cajunpanda/gameboy-hifi-audio/hardware/agb/agb-hifi-audio-fpc/agb-hifi-audio-fpc.kicad_sch

## KiCad design hardware/agb/agb-hifi-audio-fpc/agb-hifi-audio-fpc.kicad_sch (2026-06-22)

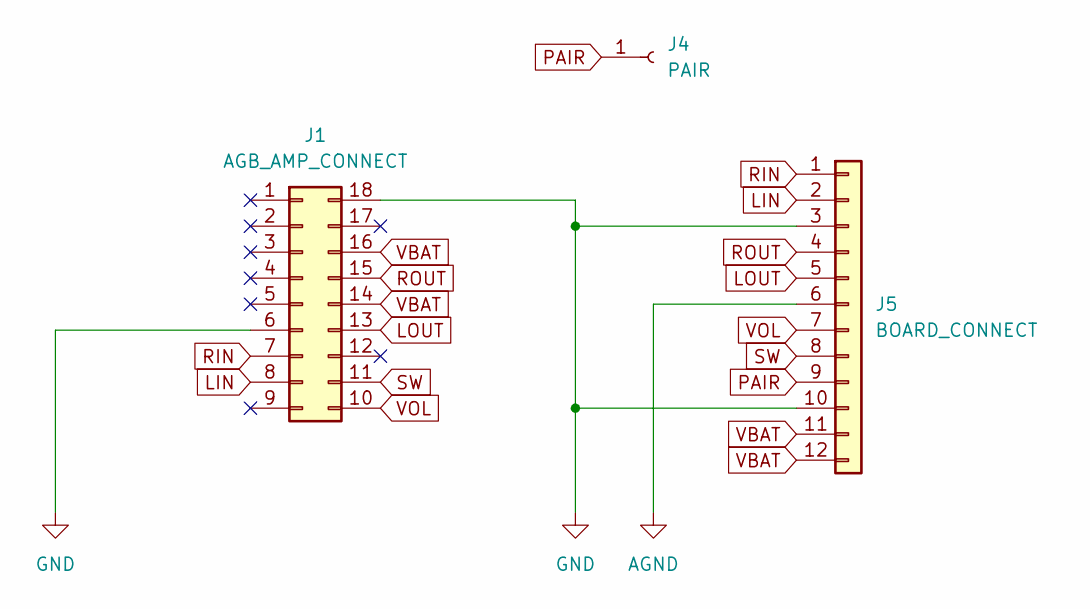
[picture p13: schematic agb-hifi-audio-fpc.kicad_sch]

Parts:
J1: AGB_AMP_CONNECT; AGB AMP CONNECT
J4: PAIR; SolderWirePad_1x01_SMD_1x2mm
J5: BOARD_CONNECT; FPC-Tail-12pos-0.5mm-FH12A

Connections:
AGND: J5.6
GND: J1.6, J1.18, J5.3, J5.10
LIN: J1.8, J5.2
LOUT: J1.13, J5.5
PAIR: J4.1, J5.9
RIN: J1.7, J5.1
ROUT: J1.15, J5.4
SW: J1.11, J5.8
VBAT: J1.14, J1.16, J5.11, J5.12
VOL: J1.10, J5.7
