cajunpanda/gameboy-hifi-audio/hardware/agb/agb-hifi-audio-pcb/agb-hifi-audio-pcb.kicad_sch

## KiCad design hardware/agb/agb-hifi-audio-pcb/agb-hifi-audio-pcb.kicad_sch (2026-07-22)

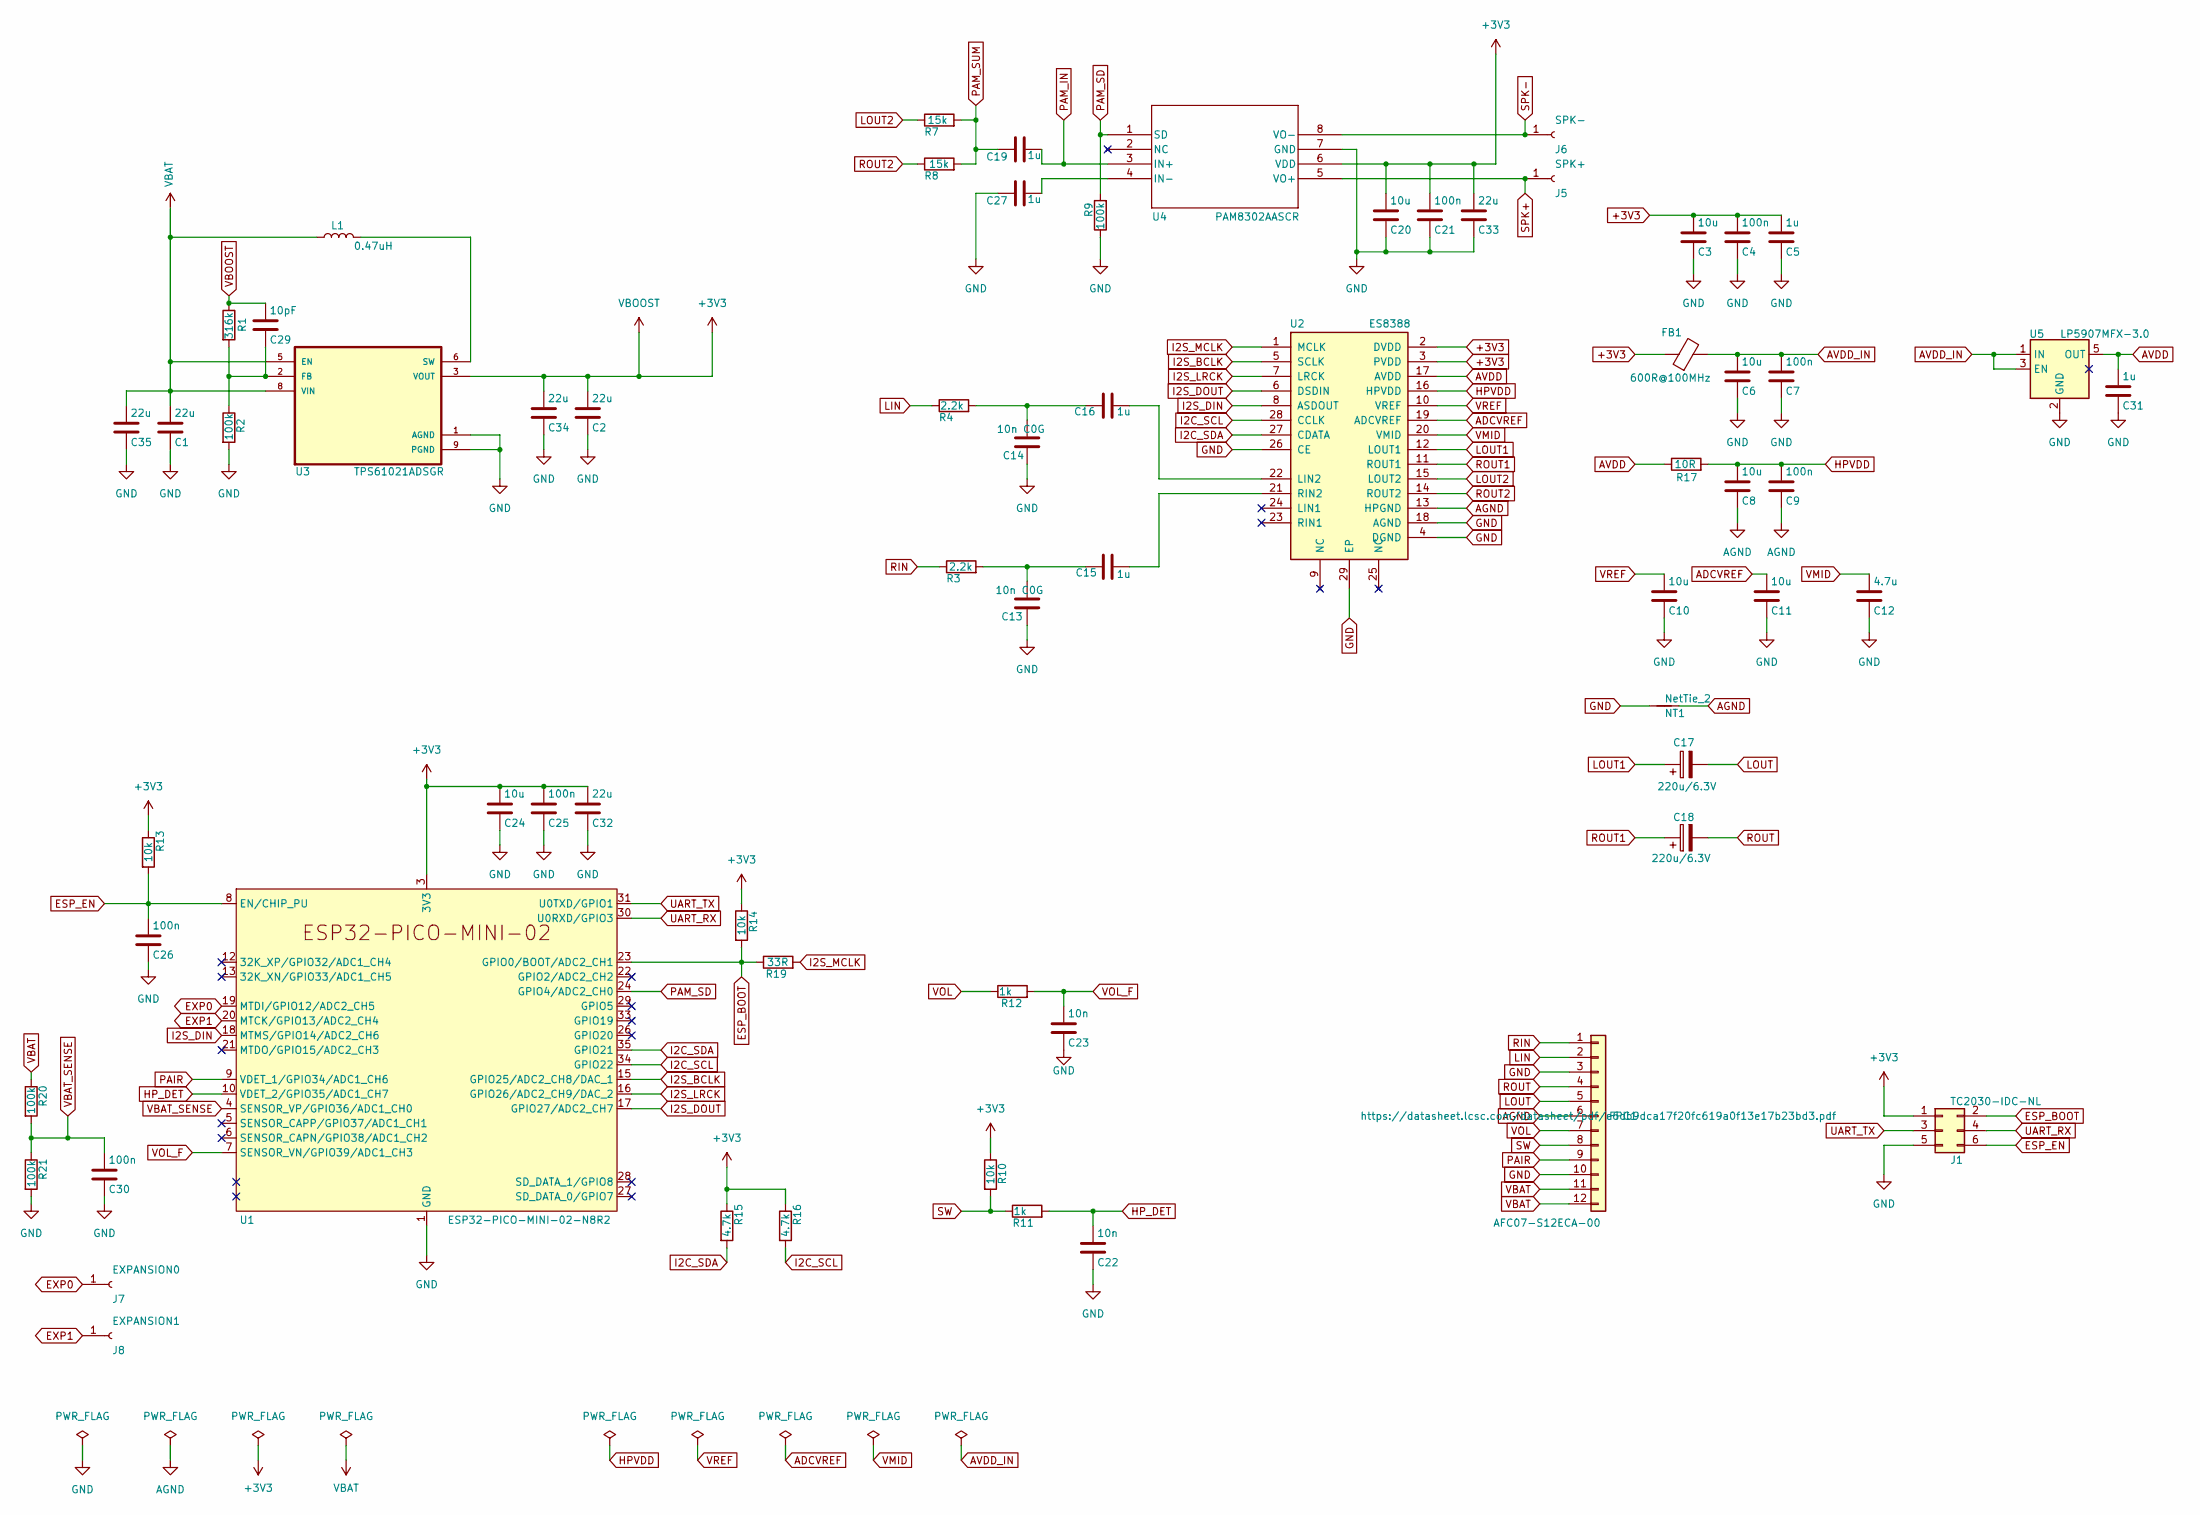
[picture p14: schematic agb-hifi-audio-pcb.kicad_sch]

Parts:
C1, C2, C32, C33, C34, C35: 22u; C_0805_2012Metric_Pad1.18x1.45mm_HandSolder; MPN CL21A226MAQNNNE; LCSC C45783
C3, C6, C8, C10, C11, C20, C24: 10u; C_0402_1005Metric_Pad0.74x0.62mm_HandSolder; MPN CL05A106MQ5NUNC; LCSC C15525
C4, C7, C9, C21, C25, C26, C30: 100n; C_0402_1005Metric_Pad0.74x0.62mm_HandSolder; MPN CL05B104KO5NNNC; LCSC C1525
C5, C15, C16, C19, C27, C31: 1u; C_0402_1005Metric_Pad0.74x0.62mm_HandSolder; MPN CL05A105KA5NQNC; LCSC C52923
C12: 4.7u; C_0402_1005Metric_Pad0.74x0.62mm_HandSolder; MPN CL05A475MP5NRNC; LCSC C23733
C13, C14: 10n C0G; C_0402_1005Metric_Pad0.74x0.62mm_HandSolder; MPN GRM1555C1E103JE01D; LCSC C3855387
C17, C18: 220u/6.3V; CP_EIA-3528-21_Kemet-B_HandSolder; MPN T520B227M006ATE045; LCSC C254404
C22, C23: 10n; C_0402_1005Metric_Pad0.74x0.62mm_HandSolder; MPN CL05B103KB5NNNC; LCSC C15195
C29: 10pF; C_0402_1005Metric_Pad0.74x0.62mm_HandSolder; MPN CL05C100JB5NNNC; LCSC C32949
FB1: 600R@100MHz; L_0402_1005Metric_Pad0.77x0.64mm_HandSolder; MPN BLM15AG601SN1D; LCSC C76884
FPC1: AFC07-S12ECA-00; FPC-SMD_12P-P0.50_AFC07-S12ECA-00; MPN AFC07-S12ECA-00; LCSC C262585
J1: TC2030-IDC-NL; Tag-Connect_TC2030-IDC-NL_2x03_P1.27mm_Vertical
J5: SPK+; SolderWirePad_1x01_SMD_1x2mm
J6: SPK-; SolderWirePad_1x01_SMD_1x2mm
J7: EXPANSION0; SolderWirePad_1x01_SMD_1x2mm
J8: EXPANSION1; SolderWirePad_1x01_SMD_1x2mm
L1: 0.47uH; L_Sunlord_SWPA252012S; MPN WIP252012P-R47ML; LCSC C964119
NT1: NetTie_2; NetTie-2_SMD_Pad0.2mm
R1: 316k; R_0402_1005Metric_Pad0.72x0.64mm_HandSolder; MPN 0402WGF3163TCE; LCSC C25777
R2, R9, R20, R21: 100k; R_0402_1005Metric_Pad0.72x0.64mm_HandSolder; MPN 0402WGF1003TCE; LCSC C25741
R3, R4: 2.2k; R_0402_1005Metric_Pad0.72x0.64mm_HandSolder; MPN 0402WGF2201TCE; LCSC C25879
R7, R8: 15k; R_0402_1005Metric_Pad0.72x0.64mm_HandSolder; MPN 0402WGF1502TCE; LCSC C25756
R10, R13, R14: 10k; R_0402_1005Metric_Pad0.72x0.64mm_HandSolder; MPN 0402WGF1002TCE; LCSC C25744
R11, R12: 1k; R_0402_1005Metric_Pad0.72x0.64mm_HandSolder; MPN 0402WGF1001TCE; LCSC C11702
R15, R16: 4.7k; R_0402_1005Metric_Pad0.72x0.64mm_HandSolder; MPN 0402WGF4701TCE; LCSC C25900
R17: 10R; R_0402_1005Metric_Pad0.72x0.64mm_HandSolder; MPN 0402WGF100JTCE; LCSC C25077
R19: 33R; R_0402_1005Metric_Pad0.72x0.64mm_HandSolder; MPN 0402WGF330JTCE; LCSC C25105
U1: ESP32-PICO-MINI-02-N8R2; MODULE_ESP32-PICO-MINI-02; MPN ESP32-PICO-MINI-02-N8R2; LCSC C2980306
U2: ES8388; QFN-28-1EP_4x4mm_P0.45mm_EP2.4x2.4mm_ThermalVias; MPN ES8388; LCSC C365736
U3: TPS61021ADSGR; DSG0008A_TEX; MPN TPS61021ADSGR; LCSC C193037
U4: PAM8302AASCR; MSOP-8_3x3mm_P0.65mm; MPN PAM8302AASCR; LCSC C113367
U5: LP5907MFX-3.0; SOT-23-5_HandSoldering; MPN LP5907MFX-3.0/NOPB; LCSC C475492

Connections:
+3V3: C1.1, C1.2, C2.1, C2.2, C3.1, C3.2, C4.1, C4.2, C5.1, C5.2, C6.1, C6.2, C7.1, C7.2, C8.1, C8.2, C9.1, C9.2, C10.1, C10.2, C11.1, C11.2, C12.1, C12.2, C13.2, C14.2, C20.1, C20.2, C21.1, C21.2, C22.2, C23.2, C24.1, C24.2, C25.1, C25.2, C26.2, C27.1, C30.2, C31.2, C32.1, C32.2, C33.1, C33.2, C34.1, C34.2, C35.1, C35.2, FB1.1, FB1.2, J1.1, J1.5, L1.1, R2.2, R9.1, R10.1, R13.1, R14.1, R15.1, R16.1, R17.2, R21.2, U1.1 (GND), U1.2 (GND), U1.3 (3V3), U1.11 (GND), U1.14 (GND), U1.36 (GND), U1.37 (GND), U1.38 (GND), U1.39 (GND), U1.40 (GND), U1.41 (GND), U1.42 (GND), U1.43 (GND), U1.44 (GND), U1.45 (GND), U1.46 (GND), U1.47 (GND), U1.48 (GND), U1.49 (GND), U1.50 (GND), U1.51 (GND), U1.52 (GND), U1.53 (GND), U1.54 (GND), U1.55 (GND), U1.56 (GND), U1.57 (GND), U1.58 (GND), U1.59 (GND), U1.60 (GND), U1.61 (GND), U2.2 (DVDD), U2.3 (PVDD), U2.10 (VREF), U2.16 (HPVDD), U2.19 (ADCVREF), U2.20 (VMID), U3.1 (AGND), U3.3 (VOUT), U3.4 (VOUT), U3.5 (EN), U3.8 (VIN), U3.9 (PGND), U4.6 (VDD), U4.7 (GND), U5.1 (IN), U5.2 (GND), U5.3 (EN)
AGND: FPC1.6, NT1.2, U2.13 (HPGND)
AVDD: C31.1, R17.1, U2.17 (AVDD), U5.5 (OUT)
ESP_BOOT: J1.2, R14.2, R19.1, U1.23 (GPIO0/BOOT/ADC2_CH1)
ESP_EN: C26.1, J1.6, R13.2, U1.8 (EN/CHIP_PU)
EXP0: J7.1, U1.19 (MTDI/GPIO12/ADC2_CH5)
EXP1: J8.1, U1.20 (MTCK/GPIO13/ADC2_CH4)
GND: FPC1.3, FPC1.10, NT1.1, U2.4 (DGND), U2.18 (AGND), U2.26 (CE), U2.29 (EP)
HP_DET: C22.1, R11.2, U1.10 (VDET_2/GPIO35/ADC1_CH7)
I2C_SCL: R16.2, U1.34 (GPIO22), U2.28 (CCLK)
I2C_SDA: R15.2, U1.35 (GPIO21), U2.27 (CDATA)
I2S_BCLK: U1.15 (GPIO25/ADC2_CH8/DAC_1), U2.5 (SCLK)
I2S_DIN: U1.18 (MTMS/GPIO14/ADC2_CH6), U2.8 (ASDOUT)
I2S_DOUT: U1.17 (GPIO27/ADC2_CH7), U2.6 (DSDIN)
I2S_LRCK: U1.16 (GPIO26/ADC2_CH9/DAC_2), U2.7 (LRCK)
I2S_MCLK: R19.2, U2.1 (MCLK)
LIN: FPC1.2, R4.1
LOUT: C17.2, FPC1.5
LOUT1: C17.1, U2.12 (LOUT1)
LOUT2: R7.1, U2.15 (LOUT2)
unnamed: C13.1, C15.1, R3.2
unnamed: C14.1, C16.1, R4.2
unnamed: C15.2, U2.21 (RIN2)
unnamed: C16.2, U2.22 (LIN2)
unnamed: C27.2, U4.4 (IN-)
unnamed: C29.2, R1.2, R2.1, U3.2 (FB)
unnamed: L1.2, U3.6 (SW), U3.7 (SW)
PAIR: FPC1.9, U1.9 (VDET_1/GPIO34/ADC1_CH6)
PAM_IN: C19.2, U4.3 (IN+)
PAM_SD: R9.2, U1.24 (GPIO4/ADC2_CH0), U4.1 (SD)
PAM_SUM: C19.1, R7.2, R8.2
RIN: FPC1.1, R3.1
ROUT: C18.2, FPC1.4
ROUT1: C18.1, U2.11 (ROUT1)
ROUT2: R8.1, U2.14 (ROUT2)
SPK+: J5.1, U4.5 (VO+)
SPK-: J6.1, U4.8 (VO-)
SW: FPC1.8, R10.2, R11.1
UART_RX: J1.4, U1.30 (U0RXD/GPIO3)
UART_TX: J1.3, U1.31 (U0TXD/GPIO1)
VBAT: FPC1.11, FPC1.12, R20.1
VBAT_SENSE: C30.1, R20.2, R21.1, U1.4 (SENSOR_VP/GPIO36/ADC1_CH0)
VBOOST: C29.1, R1.1
VOL: FPC1.7, R12.1
VOL_F: C23.1, R12.2, U1.7 (SENSOR_VN/GPIO39/ADC1_CH3)
