cajunpanda/gameboy-hifi-audio/firmware/src/dsp.c

#include "dsp.h"

#include <math.h>
#include <string.h>

#include "esp_log.h"
#include "dsps_biquad.h"
#include "dsps_biquad_gen.h"

#include "settings.h"
#include "sfx.h"

static const char *TAG = "dsp";

#define PIPE_RATE   44100.0f
#define MAX_BLOCK   256             // == audio_pipeline READ_FRAMES

// Speaker EQ band centre frequencies, voiced for the small GBA driver: a low
// shelf to tame bass the driver can't reproduce, a presence peak for clarity,
// and a high shelf for air. Band gains come from settings (dB).
#define F_BASS      (150.0f  / PIPE_RATE)
#define F_MID       (2500.0f / PIPE_RATE)
#define F_TREBLE    (5000.0f / PIPE_RATE)
#define Q_SHELF     0.707f
#define Q_PEAK      1.0f

// Per-sample one-pole smoothing for the volume gain gives click-free steps
// (~5 ms time constant at 44.1 kHz).
#define VOL_SMOOTH  0.005f

// Speaker EQ (stereo): coefficients {b0,b1,b2,a1,a2} plus a separate delay line
// {w0,w1} per channel ([0]=L, [1]=R). The local DAC path is stereo (HP), so each
// channel's biquads keep their own state.
static float s_coef_bass[5], s_coef_mid[5], s_coef_treble[5];
static float s_w_bass[2][2], s_w_mid[2][2], s_w_treble[2][2];

// Bluetooth EQ (stereo): same band coefficients, independent gains, and a
// separate delay line per channel ([0]=L, [1]=R). Each biquad instance keeps its
// own state.
static float s_bt_coef_bass[5], s_bt_coef_mid[5], s_bt_coef_treble[5];
static float s_btw_bass[2][2], s_btw_mid[2][2], s_btw_treble[2][2];

// Noise-reduction filters on the local capture path (per-channel biquad state,
// [0]=L [1]=R). Each is bypassed when its corner/center is 0 Hz; the notch is a
// fixed deep null with tunable center + Q. Tuned per GBA via the `nr` command.
static float s_nr_hpf[5], s_nr_lpf[5], s_nr_notch[5];
static float s_nr_w_hpf[2][2], s_nr_w_lpf[2][2], s_nr_w_notch[2][2];
static bool  s_nr_hpf_on, s_nr_lpf_on, s_nr_notch_on;

// Downward expander / noise gate on the local path. Envelope from each block's
// post-EQ RMS -- not peak: BLE TX bursts couple sub-ms clicks into the ADC that
// peak up to ~-37 dBFS (above any usable threshold) but carry almost no block
// energy (RMS <= -45 dBFS), while real program holds RMS near its peak (square
// waves have ~no crest factor). RMS keying gates the clicks and lets the amp
// mute engage; peak keying let every click punch through and reset the mute
// hold. Applied gain ramps per sample with a fast attack, slow release so the
// floor fades out in quiet passages without chattering. Off when threshold 0.
#define GATE_ATTACK   0.02f       // ~1 ms to open
#define GATE_RELEASE  0.0004f     // ~55 ms to close
#define GATE_MUTE_HOLD 24         // ~140 ms of sustained silence before amp mute
static bool  s_gate_on;
static float s_gate_thresh_db, s_gate_range_db;
static float s_gate_target = 1.0f;   // per-block target gain (linear)
static float s_gate_gain   = 1.0f;   // smoothed applied gain
static int   s_gate_silence = 0;     // consecutive silent blocks (amp-mute hold)
static bool  s_gate_muting = false;  // speaker-amp mute state (sustained silence)
static void (*s_gate_mute_cb)(bool) = NULL;  // notified on mute-state change

// Bluetooth-path noise reduction. The A2DP stream needs the same capture cleanup
// the local path gets: without it the raw GBA floor (hum + hiss) was fed straight
// into the SBC encoder, whose low-level rendering was audible as a distinct
// digital hash on the sink. Reuses the shared s_nr_* coefficients and gate
// thresholds (same tuning, same per-GBA `nr` settings) but keeps its own
// per-channel delay lines and its own smoothed expander gain, so the BT stream
// filters/gates independently of the local speaker path. No amp-mute here: the
// sink has its own amp, so gating the signal to silence is enough.
static float s_bt_nr_w_hpf[2][2], s_bt_nr_w_lpf[2][2], s_bt_nr_w_notch[2][2];
static float s_bt_gate_target = 1.0f;   // per-block target gain (linear)
static float s_bt_gate_gain   = 1.0f;   // smoothed applied gain

// The BT stream hard-mutes on its own threshold, more aggressive than the local
// path's expander/amp-mute, for two reasons: (1) the SBC encoder renders even a
// few-dB residual floor as audible digital hash, so BT must reach true digital
// silence where the local analog path tolerates a low floor; (2) during A2DP
// streaming the radio's conducted TX transients lift the captured floor toward
// the local gate threshold (they no longer defeat the detector outright now
// that it keys on RMS, but the margin is thin) -- this threshold sits clear of
// the floor + those transients. Below it for GATE_MUTE_HOLD blocks, the BT
// program is driven to digital zero. Runtime-tunable per GBA (settings
// nr_bt_mute_db / `nr btmute`): set it too high and quiet program (e.g. engine
// hum) gets swallowed on BT while playing fine locally; too low and the floor
// hash returns. 0 dBFS disables the hard mute (the expander still runs).
static int   s_bt_gate_silence = 0;   // consecutive below-threshold blocks (BT mute hold)
static bool  s_bt_mute_on   = true;   // BT hard mute enabled (nr_bt_mute_db < 0)
static float s_bt_mute_db   = -40.0f; // BT hard-mute threshold, dBFS

static uint32_t s_last_gen = 0xffffffffu;
// Which local-path EQ profile is live: false = Speaker EQ (HP unplugged),
// true = Headphone EQ (HP plugged). Set by dsp_set_hp_plugged(); s_hp_dirty
// forces a coeff recompute + delay-line reset on the next block even though the
// settings generation didn't change.
static volatile bool s_hp_plugged = false;
static volatile bool s_hp_dirty   = false;
static bool     s_eq_on;                 // active local EQ enabled (speaker or HP)
static bool     s_bt_eq_on;              // bluetooth EQ enabled
static float    s_vol_target = 0.0f;     // speaker volume gain target
static float    s_cur_gain = 0.0f;       // smoothed speaker volume (starts muted)
static float    s_bt_vol_target = 1.0f;  // bluetooth volume gain target
static float    s_bt_cur_gain = 1.0f;    // smoothed bluetooth volume
static float    s_sfx_gain = 0.0f;       // linear cue-mix gain (0 = sfx disabled)

// Boot startup-chime intro. While the startup clip plays, the live GBA passthrough
// (program) is muted so the clean full chime plays alone -- no doubling with the
// truncated live chime the codec picks up once the amp comes on -- and the chime
// tracks the volume wheel instead of sitting at the fixed cue level. s_intro_prog
// runs 0 (program muted, chime at wheel volume) during the intro and ramps to 1
// (program live, cues at the fixed feedback level) when the clip ends. Default 1.0
// means "no intro": normal operation is byte-for-byte unchanged. The latch is
// armed by dsp_begin_intro() before the audio task starts, then advanced only by
// the audio task in dsp_process_local(), so no locking is needed.
#define INTRO_RELEASE   0.0006f   // ~38 ms per-sample ramp back to passthrough at chime end
#define INTRO_END_GAP   12        // cue-inactive blocks (~70 ms) that mark the clip done (tolerates FIFO underruns)
#define INTRO_START_MAX 260       // ~1.5 s: if the clip never starts (missing file), give up and unmute
static bool  s_intro_active   = false;   // arming latch (clip in progress)
static bool  s_intro_cue_seen = false;   // the clip actually started
static int   s_intro_gap      = 0;       // consecutive cue-inactive blocks since start
static int   s_intro_blocks   = 0;       // blocks since arming (start-timeout)
static float s_intro_prog     = 1.0f;    // smoothed program/chime-mode gain (1 = normal)

static inline int16_t sat16(float x)
{
    if (x > 32767.0f)  x = 32767.0f;
    if (x < -32768.0f) x = -32768.0f;
    return (int16_t)lrintf(x);
}

static float db_to_lin(float db) { return powf(10.0f, db / 20.0f); }

// esp-dsp's dsps_biquad_gen_peakingEQ_f32 takes no gain argument, so the
// RBJ-cookbook peaking coefficients for the mid band are computed by hand
// (esp-dsp still runs the filter via dsps_biquad_f32). f is normalized (Fc/Fs);
// output coeffs = {b0,b1,b2,a1,a2} normalized so a0 = 1.
static void gen_peaking(float *c, float f, float gain_db, float q)
{
    float A     = powf(10.0f, gain_db / 40.0f);
    float w0    = 2.0f * (float)M_PI * f;
    float cw    = cosf(w0);
    float alpha = sinf(w0) / (2.0f * q);
    float a0    = 1.0f + alpha / A;
    c[0] = (1.0f + alpha * A) / a0;   // b0
    c[1] = (-2.0f * cw)       / a0;   // b1
    c[2] = (1.0f - alpha * A) / a0;   // b2
    c[3] = (-2.0f * cw)       / a0;   // a1
    c[4] = (1.0f - alpha / A) / a0;   // a2
}

// Recompute everything that depends on settings, only when the generation
// counter changes (coefficient generation is the expensive part). Both process
// functions call this at the top of a block; the first one does the work, the
// second sees an unchanged generation and skips. Keeps a single consistent
// snapshot per block across the speaker and BT paths.
static void maybe_recompute(void)
{
    uint32_t gen = settings_generation();
    bool hp_switch = s_hp_dirty;
    if (gen == s_last_gen && !hp_switch) return;
    s_hp_dirty = false;

    gbhifi_settings_t s;
    settings_get(&s);

    // Local-path EQ: pick the profile by which output is live (the DAC drives
    // only one; the speaker amp is muted when HP is plugged), then build the band
    // coefficients from that profile's gains. Speaker EQ voices the small GBA
    // driver; Headphone EQ is independent (flat by default).
    bool   l_on     = s_hp_plugged ? s.eq_hp_enabled   : s.eq_enabled;
    int8_t l_bass   = s_hp_plugged ? s.eq_hp_bass_db   : s.eq_bass_db;
    int8_t l_mid    = s_hp_plugged ? s.eq_hp_mid_db    : s.eq_mid_db;
    int8_t l_treble = s_hp_plugged ? s.eq_hp_treble_db : s.eq_treble_db;
    dsps_biquad_gen_lowShelf_f32 (s_coef_bass,   F_BASS,   (float)l_bass,   Q_SHELF);
    gen_peaking                  (s_coef_mid,    F_MID,    (float)l_mid,    Q_PEAK);
    dsps_biquad_gen_highShelf_f32(s_coef_treble, F_TREBLE, (float)l_treble, Q_SHELF);
    s_eq_on = l_on;

    // On a profile swap (HP plug/unplug) the delay lines hold the old filter's
    // state; flush them so the new curve doesn't ring. A settings-only change
    // (volume/EQ tweak) leaves them alone to avoid a click on every edit.
    if (hp_switch) {
        memset(s_w_bass,   0, sizeof(s_w_bass));
        memset(s_w_mid,    0, sizeof(s_w_mid));
        memset(s_w_treble, 0, sizeof(s_w_treble));
    }

    // Bluetooth EQ coefficients (same bands, independent gains).
    dsps_biquad_gen_lowShelf_f32 (s_bt_coef_bass,   F_BASS,   (float)s.eq_bt_bass_db,   Q_SHELF);
    gen_peaking                  (s_bt_coef_mid,    F_MID,    (float)s.eq_bt_mid_db,    Q_PEAK);
    dsps_biquad_gen_highShelf_f32(s_bt_coef_treble, F_TREBLE, (float)s.eq_bt_treble_db, Q_SHELF);
    s_bt_eq_on = s.eq_bt_enabled;

    // Noise-reduction filters (local path). Normalized freq = Hz / PIPE_RATE;
    // Butterworth HPF/LPF (Q=0.707), and a deep (-40 dB) notch at the tunable
    // center + Q. Zero a filter's delay line while it is off so toggling it on
    // later starts from a clean state instead of ringing on stale samples.
    s_nr_hpf_on   = s.nr_hpf_hz   > 0 && s.nr_hpf_hz   < PIPE_RATE / 2;
    s_nr_lpf_on   = s.nr_lpf_hz   > 0 && s.nr_lpf_hz   < PIPE_RATE / 2;
    s_nr_notch_on = s.nr_notch_hz > 0 && s.nr_notch_hz < PIPE_RATE / 2;
    // Zero both the local and BT delay lines when a filter is off so toggling it
    // on later starts clean on each path.
    if (s_nr_hpf_on)
        dsps_biquad_gen_hpf_f32(s_nr_hpf, (float)s.nr_hpf_hz / PIPE_RATE, Q_SHELF);
    else { memset(s_nr_w_hpf, 0, sizeof(s_nr_w_hpf));
           memset(s_bt_nr_w_hpf, 0, sizeof(s_bt_nr_w_hpf)); }
    if (s_nr_lpf_on)
        dsps_biquad_gen_lpf_f32(s_nr_lpf, (float)s.nr_lpf_hz / PIPE_RATE, Q_SHELF);
    else { memset(s_nr_w_lpf, 0, sizeof(s_nr_w_lpf));
           memset(s_bt_nr_w_lpf, 0, sizeof(s_bt_nr_w_lpf)); }
    if (s_nr_notch_on)
        dsps_biquad_gen_notch_f32(s_nr_notch, (float)s.nr_notch_hz / PIPE_RATE,
                                  -40.0f, (float)s.nr_notch_q);
    else { memset(s_nr_w_notch, 0, sizeof(s_nr_w_notch));
           memset(s_bt_nr_w_notch, 0, sizeof(s_bt_nr_w_notch)); }

    s_gate_on        = s.nr_gate_thresh_db < 0;   // 0 dBFS threshold = off
    s_gate_thresh_db = (float)s.nr_gate_thresh_db;
    s_gate_range_db  = (float)s.nr_gate_range_db;
    s_bt_mute_on     = s.nr_bt_mute_db < 0;        // 0 dBFS = BT hard mute off
    s_bt_mute_db     = (float)s.nr_bt_mute_db;

    float v   = (float)s.speaker_vol_pct / 100.0f;
    float bv  = (float)s.bt_vol_pct      / 100.0f;
    s_vol_target    = v * v;
    s_bt_vol_target = bv * bv;
    s_sfx_gain      = s.sfx_enabled ? db_to_lin((float)s.sfx_level_db) : 0.0f;

    s_last_gen = gen;
    ESP_LOGI(TAG, "recompute: spkVol=%u%% btVol=%u%% localEQ=%s:%d[%d/%d/%d] btEQ=%d[%d/%d/%d] sfx=%d",
             s.speaker_vol_pct, s.bt_vol_pct,
             s_hp_plugged ? "HP" : "spk", l_on, l_bass, l_mid, l_treble,
             s.eq_bt_enabled, s.eq_bt_bass_db, s.eq_bt_mid_db, s.eq_bt_treble_db,
             s.sfx_enabled);
}

esp_err_t dsp_init(void)
{
    maybe_recompute();
    // Seed the smoothed gains at their targets so the very first blocks aren't
    // ramping up from silence audibly.
    s_cur_gain    = s_vol_target;
    s_bt_cur_gain = s_bt_vol_target;
    ESP_LOGI(TAG, "dsp ready");
    return ESP_OK;
}

void dsp_set_hp_plugged(bool plugged)
{
    // Only flag a profile swap on an actual change. The audio task picks this up
    // in maybe_recompute() on its next block (rebuilds the local-EQ coeffs from
    // the HP-vs-speaker gains and flushes the delay lines). Plain bool writes are
    // atomic on ESP32, no lock needed.
    if (plugged != s_hp_plugged) {
        s_hp_plugged = plugged;
        s_hp_dirty   = true;
    }
}

void dsp_begin_intro(void)
{
    // Arm the startup-chime intro: mute the live passthrough from the first block so
    // the startup clip plays alone, until the clip ends (or never starts). Call
    // before audio_pipeline_start() -- i.e. before the audio task exists -- so this
    // write is not concurrent with dsp_process_local()'s reads.
    s_intro_active   = true;
    s_intro_cue_seen = false;
    s_intro_gap      = 0;
    s_intro_blocks   = 0;
    s_intro_prog     = 0.0f;   // program muted immediately (audio just started; no click)
}

void dsp_set_gate_mute_cb(void (*cb)(bool muting))
{
    s_gate_mute_cb = cb;
}

void dsp_process_local(int16_t *stereo, size_t frames)
{
    if (!stereo || frames == 0) return;
    if (frames > MAX_BLOCK) frames = MAX_BLOCK;
    maybe_recompute();

    // Deinterleave L/R/L/R into two float channels (esp-dsp biquads need
    // contiguous buffers). HP gets these as true stereo; the speaker sums them
    // passively.
    static float l[MAX_BLOCK], r[MAX_BLOCK];
    for (size_t i = 0; i < frames; i++) {
        l[i] = (float)stereo[i * 2];
        r[i] = (float)stereo[i * 2 + 1];
    }

    // Noise reduction: clean the captured signal (hum high-pass, hiss low-pass,
    // discrete-tone notch) before the voicing EQ. Each filter is skipped when off.
    if (s_nr_hpf_on) {
        dsps_biquad_f32(l, l, frames, s_nr_hpf, s_nr_w_hpf[0]);
        dsps_biquad_f32(r, r, frames, s_nr_hpf, s_nr_w_hpf[1]);
    }
    if (s_nr_lpf_on) {
        dsps_biquad_f32(l, l, frames, s_nr_lpf, s_nr_w_lpf[0]);
        dsps_biquad_f32(r, r, frames, s_nr_lpf, s_nr_w_lpf[1]);
    }
    if (s_nr_notch_on) {
        dsps_biquad_f32(l, l, frames, s_nr_notch, s_nr_w_notch[0]);
        dsps_biquad_f32(r, r, frames, s_nr_notch, s_nr_w_notch[1]);
    }

    // Speaker EQ per channel (each biquad keeps its own per-channel delay line).
    if (s_eq_on) {
        dsps_biquad_f32(l, l, frames, s_coef_bass,   s_w_bass[0]);
        dsps_biquad_f32(l, l, frames, s_coef_mid,    s_w_mid[0]);
        dsps_biquad_f32(l, l, frames, s_coef_treble, s_w_treble[0]);
        dsps_biquad_f32(r, r, frames, s_coef_bass,   s_w_bass[1]);
        dsps_biquad_f32(r, r, frames, s_coef_mid,    s_w_mid[1]);
        dsps_biquad_f32(r, r, frames, s_coef_treble, s_w_treble[1]);
    }

    // Noise gate: derive this block's target gain from its post-EQ RMS (a 2:1
    // downward expander below the threshold, floored at -range), then ramp the
    // applied gain per sample below. RMS, not peak -- see the gate note by
    // GATE_ATTACK. The program is gated; the cue is not.
    bool silent_block = false;
    if (s_gate_on) {
        float sq = 0.0f;
        for (size_t i = 0; i < frames; i++)
            sq += l[i] * l[i] + r[i] * r[i];
        float rms    = sqrtf(sq / (float)(frames * 2));
        float rms_db = (rms > 1.0f) ? 20.0f * log10f(rms / 32768.0f) : -120.0f;
        float g_db   = (rms_db >= s_gate_thresh_db) ? 0.0f
                       : fmaxf(-s_gate_range_db, 2.0f * (rms_db - s_gate_thresh_db));
        s_gate_target = db_to_lin(g_db);
        silent_block  = rms_db < s_gate_thresh_db;  // input at/under the noise floor
    } else {
        s_gate_target = 1.0f;
    }

    // The shared SFX cue mix for this block (mono cue into both channels,
    // post-volume, fixed level so cues stay audible regardless of volume). The
    // cue was rendered once for this block by sfx_generate_block(); the BT path
    // mixes the same samples. Fetched before the mute logic: the amp-mute must
    // see it.
    const float *cue = (s_sfx_gain > 0.0f && sfx_cue_active()) ? sfx_cue() : NULL;

    // Speaker-amp mute follows sustained *output* silence: program below the
    // threshold (not how deep the expander attenuates -- so it fires even when
    // the floor sits only a few dB down) AND no cue mixing in. The cue check
    // matters: cues bypass the gate, but the PAM shutdown is physical -- a chime
    // fired into a muted amp on an idle page is simply inaudible. Mute after
    // GATE_MUTE_HOLD quiet blocks; release the instant a block exceeds the
    // threshold or a cue starts. app_sm (owns PIN_PAM_SD) is called only on change.
    if (silent_block && !cue) { if (s_gate_silence < GATE_MUTE_HOLD) s_gate_silence++; }
    else                        s_gate_silence = 0;
    bool muted = (s_gate_silence >= GATE_MUTE_HOLD);
    if (s_gate_mute_cb && muted != s_gate_muting) {
        s_gate_muting = muted;
        s_gate_mute_cb(muted);
    }
    // While the amp is muted, drive the program to digital zero too: the HP amp
    // (LOUT1) has no shutdown pin, so without this a headphone listener still
    // hears the expander's -range residual -- including the BLE TX clicks --
    // through an idle page. Released the same block the silence counter resets.
    if (muted) s_gate_target = 0.0f;

    // Startup-chime intro latch (once per block): hold the passthrough muted until
    // the startup clip finishes -- cue inactive for INTRO_END_GAP blocks after it
    // started -- or bail if it never started (missing clip). s_intro_prog ramps
    // toward intro_target in the per-sample loop for a click-free hand-back.
    float intro_target = 1.0f;
    if (s_intro_active) {
        if (cue)                  { s_intro_cue_seen = true; s_intro_gap = 0; }
        else if (s_intro_cue_seen) s_intro_gap++;
        bool done  = s_intro_cue_seen && s_intro_gap >= INTRO_END_GAP;
        bool never = !s_intro_cue_seen && s_intro_blocks >= INTRO_START_MAX;
        if (done || never) s_intro_active = false;
        s_intro_blocks++;
        intro_target = s_intro_active ? 0.0f : 1.0f;
    }

    // Digital volume (perceptual squared curve, smoothed per sample so both
    // channels share the same gain) applies to the program only; the cue mixes
    // in post-volume at its fixed level.
    for (size_t i = 0; i < frames; i++) {
        s_cur_gain += (s_vol_target - s_cur_gain) * VOL_SMOOTH;
        float gc = (s_gate_target > s_gate_gain) ? GATE_ATTACK : GATE_RELEASE;
        s_gate_gain += (s_gate_target - s_gate_gain) * gc;
        s_intro_prog += (intro_target - s_intro_prog) * INTRO_RELEASE;
        // Program muted while s_intro_prog -> 0; the cue follows the wheel during the
        // intro (s_cur_gain) and blends to the fixed feedback level (s_sfx_gain) as
        // s_intro_prog -> 1. At the default s_intro_prog = 1 this is the original mix.
        float prog_g = s_cur_gain * s_gate_gain * s_intro_prog;
        float c = cue ? s_sfx_gain * (s_cur_gain + (1.0f - s_cur_gain) * s_intro_prog)
                            * cue[i]
                      : 0.0f;
        stereo[i * 2]     = sat16(l[i] * prog_g + c);
        stereo[i * 2 + 1] = sat16(r[i] * prog_g + c);
    }
}

void dsp_process_bt(int16_t *stereo, size_t frames)
{
    if (!stereo || frames == 0) return;
    if (frames > MAX_BLOCK) frames = MAX_BLOCK;
    maybe_recompute();

    // Decide whether the BT stream needs any processing this block. It passes
    // through untouched (full fidelity, cheap) only when nothing is active: BT EQ
    // off, volume at unity and settled, no cue, AND no noise reduction to run.
    // With `nr` on -- the default, so the SBC encoder isn't handed the raw capture
    // floor to render as digital hash -- nr_active holds and we always process.
    bool cue        = (s_sfx_gain > 0.0f) && sfx_cue_active();
    bool vol_active = (s_bt_vol_target < 0.999f) ||
                      (fabsf(s_bt_cur_gain - 1.0f) > 0.0005f);
    bool nr_active  = s_nr_hpf_on || s_nr_lpf_on || s_nr_notch_on || s_gate_on;
    if (!s_bt_eq_on && !vol_active && !cue && !nr_active) {
        s_bt_cur_gain = s_bt_vol_target;   // keep settled at unity, no audio touched
        return;
    }

    // Deinterleave L/R/L/R into two float channels. esp-dsp biquads operate on
    // contiguous buffers, so they can't run strided.
    static float l[MAX_BLOCK], r[MAX_BLOCK];
    for (size_t i = 0; i < frames; i++) {
        l[i] = (float)stereo[i * 2];
        r[i] = (float)stereo[i * 2 + 1];
    }

    // Noise reduction: shared coefficients with the local path, BT delay lines.
    // Strips the captured hum (HPF), hiss (LPF), and the aliased PWM whine (notch)
    // out of the stream before it reaches the SBC encoder.
    if (s_nr_hpf_on) {
        dsps_biquad_f32(l, l, frames, s_nr_hpf, s_bt_nr_w_hpf[0]);
        dsps_biquad_f32(r, r, frames, s_nr_hpf, s_bt_nr_w_hpf[1]);
    }
    if (s_nr_lpf_on) {
        dsps_biquad_f32(l, l, frames, s_nr_lpf, s_bt_nr_w_lpf[0]);
        dsps_biquad_f32(r, r, frames, s_nr_lpf, s_bt_nr_w_lpf[1]);
    }
    if (s_nr_notch_on) {
        dsps_biquad_f32(l, l, frames, s_nr_notch, s_bt_nr_w_notch[0]);
        dsps_biquad_f32(r, r, frames, s_nr_notch, s_bt_nr_w_notch[1]);
    }

    // EQ (per channel, each biquad keeps its own delay line).
    if (s_bt_eq_on) {
        dsps_biquad_f32(l, l, frames, s_bt_coef_bass,   s_btw_bass[0]);
        dsps_biquad_f32(l, l, frames, s_bt_coef_mid,    s_btw_mid[0]);
        dsps_biquad_f32(l, l, frames, s_bt_coef_treble, s_btw_treble[0]);
        dsps_biquad_f32(r, r, frames, s_bt_coef_bass,   s_btw_bass[1]);
        dsps_biquad_f32(r, r, frames, s_bt_coef_mid,    s_btw_mid[1]);
        dsps_biquad_f32(r, r, frames, s_bt_coef_treble, s_btw_treble[1]);
    }

    // Noise gate: same downward-expander law as the local path (target from this
    // block's post-EQ RMS -- not peak, see the gate note by GATE_ATTACK), its own
    // smoothed gain. Fades the program to silence in quiet passages so the
    // encoder sees true silence instead of the low-level floor. No amp-mute side
    // effect -- that is the local speaker's concern.
    if (s_gate_on) {
        float sq = 0.0f;
        for (size_t i = 0; i < frames; i++)
            sq += l[i] * l[i] + r[i] * r[i];
        float rms    = sqrtf(sq / (float)(frames * 2));
        float rms_db = (rms > 1.0f) ? 20.0f * log10f(rms / 32768.0f) : -120.0f;
        float g_db   = (rms_db >= s_gate_thresh_db) ? 0.0f
                       : fmaxf(-s_gate_range_db, 2.0f * (rms_db - s_gate_thresh_db));
        s_bt_gate_target = db_to_lin(g_db);
        // Sustained silence below the BT mute threshold: hard-mute to true digital
        // zero rather than the expander's partial floor, so the encoder sees actual
        // silence (not a -few-dB residual it renders as hash). Own counter/threshold
        // (see BT_MUTE_THRESH_DB) so it fires on the low-level GBA floor -- which
        // parks near the local gate threshold and, with the TX transients, never
        // trips the shared silence detector -- independently of the local amp-mute.
        if (s_bt_mute_on && rms_db < s_bt_mute_db) {
            if (s_bt_gate_silence < GATE_MUTE_HOLD) s_bt_gate_silence++;
        } else {
            s_bt_gate_silence = 0;
        }
        if (s_bt_mute_on && s_bt_gate_silence >= GATE_MUTE_HOLD) s_bt_gate_target = 0.0f;
    } else {
        s_bt_gate_target = 1.0f;
        s_bt_gate_silence = 0;
    }

    // Digital volume (smoothed per sample, click-free) x the gate gain, then the
    // shared SFX cue mix (post-volume/gate, fixed level -- cues are not gated, same
    // as the local path).
    const float *cue_buf = cue ? sfx_cue() : NULL;
    for (size_t i = 0; i < frames; i++) {
        s_bt_cur_gain += (s_bt_vol_target - s_bt_cur_gain) * VOL_SMOOTH;
        float gc = (s_bt_gate_target > s_bt_gate_gain) ? GATE_ATTACK : GATE_RELEASE;
        s_bt_gate_gain += (s_bt_gate_target - s_bt_gate_gain) * gc;
        float c = cue_buf ? s_sfx_gain * cue_buf[i] : 0.0f;
        stereo[i * 2]     = sat16(l[i] * s_bt_cur_gain * s_bt_gate_gain + c);
        stereo[i * 2 + 1] = sat16(r[i] * s_bt_cur_gain * s_bt_gate_gain + c);
    }
}
